fliperama86/neopico-hd/docs/GENLOCK.md

# Genlock — Implementation Analysis

## Problem

MVS runs at ~59.18 Hz. HDMI output at 60 Hz causes periodic frame repeats (~every 2s), visible as stutter in scrolling games.

---

## Option 1: Hardware Genlock (XIN Replacement)

Replace the RP2350's 12 MHz crystal with the MVS 12 MHz clock. Since the PLL is hardwired to XOSC, feeding MVS 12 MHz directly into XIN makes the entire system clock tree phase-locked to the Neo Geo — true hardware genlock with **zero software changes** to clock configuration.

### Why 12 MHz

The MVS master clock is 24 MHz; a 12 MHz derived clock is available on the board. This matches the RP2350's crystal frequency exactly, so all existing PLL divider settings (FBDIV, POSTDIV1, POSTDIV2) stay identical.

### PCB Changes

1. **Do not populate** the 12 MHz crystal
2. **Route MVS 12 MHz** to the **XIN pin** with signal conditioning:

```
MVS 12MHz ──[100R]──┬── XIN
                     │
                   [47pF]
                     │
                    GND
```

3. **XOUT**: leave floating or tie through 1M to XIN

### XOSC Configuration

Configure XOSC in bypass/external clock mode:

```c
xosc_hw->ctrl = XOSC_CTRL_FREQ_RANGE_VALUE_1_15MHZ;
hw_set_bits(&xosc_hw->ctrl, XOSC_CTRL_ENABLE_VALUE_ENABLE << XOSC_CTRL_ENABLE_LSB);
```

### What This Gets You

- **PLL_SYS config unchanged**: 12 MHz × FBDIV / POSTDIV = 126 MHz (same as today)
- **clk_sys, clk_hstx, PIO clocks** — everything phase-locked to MVS
- **Zero drift**: no frame repeats, no stutter in scrollers
- **No software genlock logic needed**
- **Audio coherence**: pixel clock and audio timing are synchronous from the first frame

### Concerns

1. **No MVS = No Boot**: Accept it, use ROSC fallback, or add a CMOS mux (SN74LVC1G3157) to switch between crystal and MVS 12 MHz.
2. **Startup Sequencing**: XOSC has a built-in stabilization counter. ROSC can serve as initial clock if there's a race.
3. **Signal Quality**: XIN accepts CMOS square waves. 100R + 47pF filters ringing. PLL VCO provides jitter filtering.
4. **Cold Boot Audio**: May improve — HDMI output is synchronous from the first frame.

---

## Option 2: Dynamic VTOTAL Modulation (Software, `NEOPICO_EXP_GENLOCK_DYNAMIC`)

Implemented, removed in the 2026-07-31 flag sunset, and **resurrected
2026-08-01** (default OFF) to fix the ~1.2 s horizontal-scroll hiccup: the
free-running ~60 Hz output beats against the 59.186 Hz MVS and repeats one
input frame per beat. The restored implementation is the bench-tuned
pre-sunset servo (wide-hysteresis ±1 vtotal acquire, constant-vtotal steady
state with a rate-limited sub-line vblank h-trim integrator), not the simple
sketch below, which is kept as the design reference.

Resurrection notes:

- Nominal vtotals: 532 (480p), 266 (240p), **751** (720p). The pre-sunset
  720p nominal 762 belonged to the deleted 372 MHz 1650-h_total timing; the
  exact-clock 1440×741 @ 64 MHz mode needs 751 (16 897.5 µs/frame vs the
  16 896.0 µs MVS frame, residual ~1.5 µs/frame, well inside the ±30 px trim
  authority of ~14.5 µs/frame over 31 vblank lines).
- scratch_x content plus the 2 KiB core-1 stack fill that bank EXACTLY; the
  genlock build therefore moves the vsync callback (which inlines the servo)
  to scratch_y via `VIDEO_PIPELINE_VSYNC_RAM` (video_pipeline.h). The
  default build keeps scratch_x placement and is byte-identical to
  pre-resurrection firmware.
- Nominals are MVS-tuned: a SNES build compiles but cannot lock to the SNES's
  ~60.10 Hz (true pre-sunset as well; SNES remains best-effort).
- Telemetry: root menu → Genlock (phase/trim/slots/vtotal/uptime + perf
  probe). Not yet hardware-validated post-resurrection; the output refresh
  becomes ~59.19 Hz, outside CTA's ±0.5 %, which the user has accepted as a
  compatibility trade-off.

The professional scan converter approach. No hardware changes needed. Measures the phase relationship between MVS and HDMI VSYNCs in real-time and modulates `v_total_lines` by ±1 to track.

### How It Works

1. On each **MVS VSYNC** (Core 0, `video_capture_run` loop), snapshot a free-running timer
2. On each **HDMI VSYNC** (Core 1, `vsync_callback`), snapshot the same timer
3. Compute phase difference: `hdmi_vsync_time - mvs_vsync_time`
4. If HDMI is ahead (phase drifting positive) → set `rt_v_total_lines = 526` for one frame (slow down)
5. If HDMI is behind (phase drifting negative) → set `rt_v_total_lines = 524` for one frame (speed up)
6. Otherwise → keep nominal `rt_v_total_lines = 525`

### Why It Works

The DMA ISR already reads `rt_v_total_lines` directly every scanline:

```c
v_scanline = (v_scanline + 1) % rt_v_total_lines;
```

Writing `rt_v_total_lines` is a single `uint16_t` store — atomic on ARM. No need to disable IRQs, rebuild command lists, or resync HSTX. The ISR picks up the new value on the next wrap.

### Implementation Sketch

```c
// Shared between cores (written by Core 0, read by Core 1)
static volatile uint32_t g_mvs_vsync_timestamp;

// Core 0 — video_capture_run(), on each MVS VSYNC:
g_mvs_vsync_timestamp = timer_hw->timerawl;

// Core 1 — vsync_callback(), on each HDMI VSYNC:
uint32_t mvs_ts = g_mvs_vsync_timestamp;
uint32_t hdmi_ts = timer_hw->timerawl;
int32_t phase_us = (int32_t)(hdmi_ts - mvs_ts);

// Dead zone prevents oscillation
#define GENLOCK_THRESHOLD_US 200
if (phase_us > GENLOCK_THRESHOLD_US) {
    rt_v_total_lines = 526;  // stretch — slow down HDMI
} else if (phase_us < -GENLOCK_THRESHOLD_US) {
    rt_v_total_lines = 524;  // shrink — speed up HDMI
} else {
    rt_v_total_lines = 525;  // nominal
}
```

### Advantages Over Static Genlock

| | Static Genlock | Dynamic VTOTAL |
|---|---|---|
| Compile-time config | Required | Not needed |
| Tracks real MVS clock | No (assumes fixed fps) | Yes (measured per-frame) |
| Handles clock drift | No | Yes |
| Pixel clock | Non-standard | Standard 25.2 MHz |
| ACR packets | Need custom CTS | Standard CTS |
| TV compatibility | Most TVs accept it | Better (standard pixel clock) |
| Visible artifact | Stutter if estimate is off | Invisible (1-line = 0.19%) |

### Design Considerations

- **Hysteresis**: The ±200µs dead zone prevents hunting. Tune on hardware — too tight causes oscillation, too wide allows visible drift before correction.
- **Max modulation**: ±1 line per frame only. Larger jumps risk visible glitch.
- **Audio packet scheduling**: `hstx_di_queue` uses `cached_v_total_lines` for audio scheduling. Keep this at nominal (525); ±1 line modulation is negligible for audio timing.
- **Phase wraparound**: Signed subtraction of uint32 handles timer wraparound naturally.
- **240p mode**: Same principle applies but with `rt_v_total_lines` based on 262 (±1 → 261 or 263).
- **Enable/disable**: Should be feature-flagged and toggleable at runtime (e.g., OSD menu option).

### Existing Infrastructure

The codebase already has everything needed:

- `video_frame_count` — HDMI frame counter (Core 1)
- `g_frame_count` — MVS frame counter (Core 0)
- `vsync_callback` — called on every HDMI VSYNC (Core 1)
- `rt_v_total_lines` — directly used in DMA ISR, writable at any time
- `timer_hw->timerawl` — free-running µs timer, accessible from both cores

---

## Option 3: Static Sysclk Match (Deleted Experiment)

Adjusted sysclk at boot to approximate the MVS frame rate. Simple, mostly worked, but:
- Not phase-locked — would still drift if the MVS clock differed from the assumed value
- Non-standard pixel clock requires custom ACR CTS
- Compile-time only — can't adapt to different boards

Removed from the firmware (dead experiment; never combined with the dynamic
VTOTAL genlock below, which was also removed after being implemented and then
not pursued further).

### Alternative: VTOTAL Match (Static, also deleted)

Kept pixel clock standard but inflated the back porch. Same limitations as
static sysclk (no feedback). Also removed.

---

## RP2350 Clock System Quick Reference

| Feature | Status | Details |
|---|---|---|
| External clock on XIN | Yes | CMOS-level, bypass mode |
| PLL FBDIV dynamic adjust | Yes | While locked, may overshoot/undershoot |
| PLL POSTDIV dynamic adjust | No | Requires unlock |
| GPIN clock input | Yes | GP12,14,20,22 — 50 MHz max, divide only |
| GPIN → PLL reference | No | PLL hardwired to XOSC/XIN |
| HSTX fractional divider | No | Integer only |
| Frequency counter (FC0) | Yes | Built-in, configurable accuracy |

## Recommendation

1. **Done (2026-08-01)**: dynamic VTOTAL modulation is back as
   `NEOPICO_EXP_GENLOCK_DYNAMIC` (default OFF; see Option 2 resurrection
   notes). Pending hardware soak before any default flip.
2. **Next PCB rev**: Add MVS 12 MHz → XIN option for true hardware genlock.
