fliperama86/neopico-hd/docs/HSTX_IMPLEMENTATION.md

# HDMI & HSTX Implementation Reference

Comprehensive record of the RP2350 HSTX implementation and HDMI audio findings.

## 1. System Architecture

- **Core 0**: Handles pixel-perfect video capture (PIO1+DMA). The stable path uses one 32K-entry RGB565 LUT. The optional Colors menu keeps two such LUTs and selects one pointer at input VSYNC, with the same one-read pixel loop. A separate default-off DARK/SHADOW experiment uses an 8.25 KiB split LUT and is timing-regressed on hardware.
- **Core 1**: Dedicated to HSTX HDMI output and the audio pipeline (polling PIO2, SRC, and TERC4 encoding).
- **Inter-core**: Single 320x240 RGB565 framebuffer + Audio Ring Buffer.

## 2. HSTX Video Pipeline

### Output Timings

- **640x480 Pixel Clock**: 25.2 MHz. The selector runs the CPU at 252 MHz and divides `clk_hstx` by 2, then the HSTX serializer by 5.
- **640x480 Line Length**: Exactly 800 pixel clocks for the VGA timing.
- **Runtime 1280x720 Pixel Clock**: exactly 64.000 MHz from a 320 MHz
  system/HSTX clock. The 1440x741 reduced-blanking raster runs at 59.979 Hz,
  uses H+/V- sync, and advertises VIC 0 with an explicit 16:9 aspect. This is
  the only 720p path; the former fixed compile-time 720p mode and its
  74.4 MHz / 372 MHz non-RT comparison path have been deleted, along with the
  experimental 960x720/1024x768 PC-monitor modes.
- **Command Lists**: Uses `HSTX_CMD_RAW_REPEAT` for blanking and `HSTX_CMD_TMDS` for active pixels.
- **NOPs**: `HSTX_CMD_NOP` separators are used to manage hardware state transitions.

### Sync Polarity

- The runtime engine tracks horizontal and vertical polarity separately.
- For a negative-polarity signal, the wire bit is low during the active pulse.
- TMDS control symbols:
  - `0x354u`: $V=0, H=0$
  - `0x0abu`: $V=0, H=1$
  - `0x154u`: $V=1, H=0$
  - `0x2abu`: $V=1, H=1$

### Stability & Scaling

- **RAW_N_SHIFTS**: Must be set to **1** in the HSTX command expander. A value of 0 actually means 32 shifts, which causes massive horizontal sync drift.
- **Line Doubling**: The 240p MVS source is scaled to 480p by doubling every line (`fb_line = dvi_line >> 1`). This ensures the full HDMI active area is filled with stable data.

### Native 240p AVI Compatibility

The native 240p output uses a non-CEA 1280x240 timing with VIC 0. Production builds define `PICO_HDMI_LEGACY_240P_AVI_INFOFRAME=1`, which emits the hardware-validated conservative AVI payload (`PB1=0x00`, `PB2=0x08`, `PR=0`). The active-format/aspect payload with `PR=3` caused black video with continuing HDMI audio on tested scaler paths. This compatibility behavior is limited to the 240p descriptor. Standard 480p retains its normal metadata, while exact-clock 720p independently uses VIC 0 with an explicit 16:9 aspect.

## 3. HDMI Audio (Data Islands)

### Encoding

- **Mode**: TERC4 (4-bit to 10-bit).
- **Structure**: 36 pixel clocks (2 Guard + 32 Packet + 2 Guard).
- **Placement**: Mode-dependent. The VGA, 240p, and PC descriptors place Data
  Islands within horizontal sync; 1280x720 uses the back porch.

### Critical Discoveries

1. **Validity Bit (V)**: MUST be set to **0 (Valid)**. Most TVs mute if $V=1$.
2. **ACR Packet**: Byte order is **Big Endian**.
   - $N = 6144$
   - $CTS = 25200$ at a 25.2 MHz pixel clock
   - $CTS = 64000$ at the exact-clock 64 MHz 720p pixel clock
3. **Throughput**: Sending packets on active video lines is required to meet the 48kHz rate (~200 packets/frame).
4. **Header Flag**: The very first symbol of the first header byte correctly omits the Data Island flag (bit 3) for compatibility.

### Pacing & Clock Accuracy

Audio packets are paced by a per-scanline accumulator in `hstx_di_queue_tick()`. The samples-per-line value is derived from the actual pixel clock and `h_total`, never from an assumed 60 Hz field rate (an early version assumed exactly 60 Hz, which over-delivered ~91 samples/s at 240p's 60.114 Hz and caused periodic dropouts; fixed in pico_hdmi `e2a4022`).

That fix still floor-truncated the value to 16.16 fixed point, delivering slightly fewer samples than the ACR-advertised rate on the same clock: about 0.18 samples/s short at 480p/240p and roughly 0.1 at the former 720p timing. Since ACR (N=6144, CTS=pixel_clock/1000, integer-exact for 25.2, 64.0, and 74.4 MHz) tells the sink to play exactly 48000 Hz, the sink's buffer drains slowly and conceals with a brief mute: a rare, TV-dependent audio drop every tens of minutes.

Since pico_hdmi `b6422ee`, `PICO_HDMI_EXACT_AUDIO_PACING` (default **ON**) carries the exact division remainder in a rational (Bresenham) accumulator, so long-term delivery equals the nominal sample rate exactly, with bounded 1/65536-sample jitter. The runtime and non-RT paths both honor this option. Rollback: build with `-DPICO_HDMI_EXACT_AUDIO_PACING=OFF`.

### Underrun Diagnostics

If the producer (Core 1 audio task) cannot keep the Data Island queue non-empty, the scanline ISR splices a pre-encoded 4-sample silence packet and increments `hstx_di_queue_silence_count`. Build with `-DNEOPICO_DIAG_AUDIO_OSD=ON` (default OFF) to display this counter as `AU<n>` on the selftest OSD screen: a counter that climbs while a drop is heard means producer starvation; a flat counter means the drop happened inside the sink.

## 4. Hardware Resource Mapping (RP2350B)

| Peripheral | Purpose | GPIO Range |
| --- | --- | --- |
| **HSTX** | HDMI Output | 12-19 |
| **PIO1** | Video Capture | 27-45 (Bank 1) |
| **PIO2** | I2S Audio | 0-2 (Bank 0) |

### External Connection Requirements

- **HDMI +5V**: Pin 18 on the HDMI connector MUST be powered with 5V.
- **Compatibility Note**: While the Morph4K may work without it, the RetroTINK and many TVs require this for signal detection.

## 5. Reference References

- `pico_lib` (Shuichi Takano): Original HDMI audio logic.
- `hsdaoh-rp2350` (Steve Markgraf): HSTX Data Island proof-of-concept.
