fliperama86/neopico-hd/docs/STREAMING_PIPELINE_PLAN.md

# NeoPico-HD: Line-Streaming Pipeline

## Current Status

**Working:** 256-line ring buffer with soft frame sync. Video stable, audio working.

**Memory:** ~241 KB BSS (down from ~417 KB original)

---

## Architecture

```
ORIGINAL (Frame-buffered + LUT):
  Core 0: Capture full frame → large LUT conversion → framebuf[320x240]
  Core 1: ISR reads framebuf → HDMI output
  Memory: ~417 KB

CURRENT (256-line ring buffer):
  Core 0: Capture line → direct RGB555→RGB565 → ring[256 lines]
  Core 1: ISR reads from ring → HDMI output
  On output VSYNC: Sync read position to latest input frame
  Memory: ~241 KB
```

---

## How It Works

### Line Ring Buffer

The ring buffer holds 256 lines (more than one full 224-line frame):

- **Core 0 (Producer):** Writes captured MVS lines sequentially
- **Core 1 (Consumer):** Reads lines for HDMI output with 2x scaling

### Frame Synchronization

At each **output VSYNC**, Core 1 syncs its read position to the latest input frame:

```c
// Called at output VSYNC
static inline void line_ring_output_vsync(void) {
    g_line_ring.read_frame_start = g_line_ring.frame_base_idx;
}
```

This approach:
- Allows independent input/output clocks (~59.6 Hz vs ~60 Hz)
- Occasionally duplicates or skips a frame to maintain sync
- No visible tearing due to full-frame buffer margin

---

## 40-Line Streaming Attempt (Shelved)

We investigated reducing the buffer to 40 lines inspired by cps2_digiav's approach.

**Motivation:** Raw performance for OSD rendering, not memory savings. A tighter streaming pipeline would provide more predictable timing and reduce memory bandwidth contention during scanline processing.

### What We Tried

1. **HSTX Hard Reset on Input VSYNC**
   - Reset HSTX shift register and clock generator via CSR.EN toggle
   - **Result:** Display lost signal entirely

2. **Soft Resync (flag only)**
   - Just sync read position without HSTX reset
   - **Result:** Flickering - 40-line buffer too small for phase variation

3. **Clock Adjustment (125 MHz)**
   - Slow output to ~59.5 Hz so it trails input
   - **Result:** Still flickering - phase mismatch within frames

### Why It Failed

The fundamental issue: with only 40 lines of buffer, the phase relationship between input and output VSYNC must be tightly controlled. Without hardware genlock:

- Output VSYNC timing is independent of input
- Phase can drift by tens of lines within a frame
- 40 lines isn't enough margin for worst-case phase offset

### cps2_digiav Difference

cps2_digiav uses an FPGA with precise control over output timing. Their `V_STARTLINE` mechanism can instantly reposition the output scanline counter. The RP2350's HSTX doesn't support mid-stream repositioning without losing signal.

### Future Options

If 40-line streaming is revisited:
1. **PLL-based genlock:** Lock output pixel clock to input (complex)
2. **Frame skip detection:** Predict phase and pre-adjust
3. **Larger minimum buffer:** Find the threshold (64? 80? 128 lines?)

---

## Memory Budget

| Component | Size |
|---|---|
| line_ring (256 lines) | 164 KB |
| Audio buffers | ~8 KB |
| Other (stacks, DMA, etc.) | ~69 KB |
| **Total BSS** | **~241 KB** |

The RP2350 has 520 KB SRAM, leaving ~279 KB free for future features (OSD, settings, etc.).

---

## Files

| File | Purpose |
|---|---|
| `src/video/line_ring.h` | Ring buffer API and data structure |
| `src/video/video_capture.c` | Core 0 capture loop, writes to ring |
| `lib/pico_hdmi/src/video_output.c` | Core 1 HDMI output, reads from ring |
| `src/main.c` | Scanline callback with 2x scaling |

---

## DARK/SHADOW Status

Current implementation:

1. PIO capture preserves 19 bits including SHADOW and DARK.
2. Default build (`NEOPICO_ENABLE_DARK_SHADOW=OFF`) uses a 32K-entry RGB LUT path and does not apply the captured SHADOW/DARK flags.
3. Whenever DARK/SHADOW is off (MVS builds), the live persistent Colors menu adds `Digital` and `Analog` normal-color choices. Two 64 KiB tables are generated at boot, and browsing previews through one frame-stable pointer selected at input VSYNC. SELECT restores the committed model; START/MENU persists the preview. The pixel loop still performs one LUT read and ignores SHADOW/DARK.
4. Separate `NEOPICO_ENABLE_DARK_SHADOW=ON` uses an 8,448-byte split RGB565 LUT with four independent states. Hardware testing showed bottom-screen pixel jitter, so it remains default off; enabling it automatically compiles out the Colors menu (the two features share the same capture LUT machinery).
