fliperama86/neopico-hd/src/video/line_ring.h

#ifndef LINE_RING_H
#define LINE_RING_H

#include "hardware/sync.h"

#include <stdbool.h>
#include <stdint.h>

#include "capture_profile.h"

// Line buffer configuration. Fixed board/tuning constant, not a build
// variant (was NEOPICO_LINE_RING_SIZE; see AGENTS.md flag-sunset notes).
#define NEOPICO_LINE_RING_SIZE 256

#define LINE_RING_SIZE NEOPICO_LINE_RING_SIZE
#define LINE_WIDTH CAPTURE_FRAME_WIDTH
#define LINES_PER_FRAME CAPTURE_ACTIVE_HEIGHT

typedef struct {
    uint16_t lines[LINE_RING_SIZE][LINE_WIDTH]; // ~25KB line buffer

#if NEOPICO_EXP_RGB888_SCANOUT
    // RGB888 scanout stores raw entropy (DARK + raw RGB555) in the 16 bits
    // above, which leaves no room for SHADOW. SHADOW is a screen-wide control
    // (system latch bit 0), so one flag per line is faithful and costs 256 B.
    uint8_t line_shadow[LINE_RING_SIZE];
#endif

    // Core 0 (producer) state
    volatile uint32_t write_idx;      // Global write position (lines written total)
    volatile uint32_t frame_base_idx; // Global index where current frame starts

    // Core 1 (consumer) state
    volatile uint32_t read_frame_start; // Global index of display frame start

    // Resync flag - Core 0 requests, Core 1 executes
    volatile bool resync_pending;
} line_ring_t;

extern line_ring_t g_line_ring;

// ============================================================================
// Diagnostic counters (NEOPICO_DIAG_COUNTERS, default OFF) — capture-health
// instrumentation for the 720p glitch investigation. Dumped over USB-serial.
// ============================================================================
#ifndef NEOPICO_DIAG_COUNTERS
#define NEOPICO_DIAG_COUNTERS 0
#endif

#if NEOPICO_DIAG_COUNTERS
typedef struct {
    volatile uint32_t not_written; // Core 1 wanted a line the producer hadn't written yet
    volatile uint32_t overrun;     // Core 1 wanted a line already overwritten (ring wrap)
    volatile uint32_t out_frames;  // Core 1 output VSYNCs
    volatile uint32_t sync_resets; // Core 0 capture hardware resets (MVS signal loss)
} line_ring_diag_t;
extern line_ring_diag_t g_line_ring_diag;
#endif

// ============================================================================
// Core 0 API (Producer) - Input capture side
// ============================================================================

// Called at input VSYNC - request HSTX resync
static inline void line_ring_vsync(void)
{
    // Mark start of new frame
    g_line_ring.frame_base_idx = g_line_ring.write_idx;
    __dmb();
    // Request Core 1 to resync HSTX
    g_line_ring.resync_pending = true;
}

// Get write pointer for line N within current frame
static inline uint16_t *line_ring_write_ptr(uint16_t line)
{
    uint32_t idx = g_line_ring.frame_base_idx + line;
    return g_line_ring.lines[idx % LINE_RING_SIZE];
}

// Signal that lines 0..(total_lines-1) of current frame are written
static inline void line_ring_commit(uint16_t total_lines)
{
    __dmb(); // Ensure line data visible before updating index
    g_line_ring.write_idx = g_line_ring.frame_base_idx + total_lines;
}

// ============================================================================
// Core 1 API (Consumer) - HDMI output side
// ============================================================================

// Check if resync is requested (called from DMA ISR)
// Only clears the flag - actual sync happens at output VSYNC via line_ring_output_vsync()
static inline bool line_ring_should_resync(void)
{
    if (g_line_ring.resync_pending) {
        g_line_ring.resync_pending = false;
        return true;
    }
    return false;
}

// Called at output VSYNC (when not resyncing)
static inline void line_ring_output_vsync(void)
{
    uint32_t frame_start = g_line_ring.frame_base_idx;
    __dmb();
    const uint32_t write_pos = g_line_ring.write_idx;

    // Core 0 publishes the new frame base before it commits line 0. If HDMI
    // lands in that short window, retain the previous complete frame instead
    // of selecting an empty frame and emitting fallback-colored lines.
    if (write_pos == frame_start && frame_start >= LINES_PER_FRAME) {
        frame_start -= LINES_PER_FRAME;
    }
    g_line_ring.read_frame_start = frame_start;
    __dmb();
#if NEOPICO_DIAG_COUNTERS
    g_line_ring_diag.out_frames++;
#endif
}

// Check if line is ready and still in buffer
static inline bool line_ring_ready(uint16_t line)
{
    uint32_t target_idx = g_line_ring.read_frame_start + line;
    uint32_t write_pos = g_line_ring.write_idx;

    // Line must have been written
    if (target_idx >= write_pos) {
#if NEOPICO_DIAG_COUNTERS
        g_line_ring_diag.not_written++;
#endif
        return false; // Not written yet
    }

    // Line must still be in buffer (not overwritten)
    if (write_pos - target_idx > LINE_RING_SIZE) {
#if NEOPICO_DIAG_COUNTERS
        g_line_ring_diag.overrun++;
#endif
        return false; // Buffer overrun - data was overwritten
    }

    return true;
}

// Get read pointer for line N in current display frame
static inline const uint16_t *line_ring_read_ptr(uint16_t line)
{
    __dmb(); // Ensure we see latest committed data
    uint32_t target_idx = g_line_ring.read_frame_start + line;
    return g_line_ring.lines[target_idx % LINE_RING_SIZE];
}

#if NEOPICO_EXP_RGB888_SCANOUT
static inline void line_ring_write_shadow(uint16_t line, uint32_t shadow)
{
    uint32_t target_idx = g_line_ring.frame_base_idx + line;
    g_line_ring.line_shadow[target_idx % LINE_RING_SIZE] = (uint8_t)(shadow & 1U);
}

static inline uint32_t line_ring_read_shadow(uint16_t line)
{
    uint32_t target_idx = g_line_ring.read_frame_start + line;
    return g_line_ring.line_shadow[target_idx % LINE_RING_SIZE];
}
#endif

#endif // LINE_RING_H
