fliperama86/neopico-hd/src/misc/debug_render.c

#include "debug_render.h"
#include <string.h>

// Standard 5x7 font (ASCII 32-126)
static const uint8_t font_5x7[] = {
    0x00, 0x00, 0x00, 0x00, 0x00, // 32 space
    0x00, 0x00, 0x5f, 0x00, 0x00, // 33 !
    0x00, 0x07, 0x00, 0x07, 0x00, // 34 "
    0x14, 0x7f, 0x14, 0x7f, 0x14, // 35 #
    0x24, 0x2a, 0x7f, 0x2a, 0x12, // 36 $
    0x23, 0x13, 0x08, 0x64, 0x62, // 37 %
    0x36, 0x49, 0x55, 0x22, 0x50, // 38 &
    0x00, 0x05, 0x03, 0x00, 0x00, // 39 '
    0x00, 0x1c, 0x22, 0x41, 0x00, // 40 (
    0x00, 0x41, 0x22, 0x1c, 0x00, // 41 )
    0x14, 0x08, 0x3e, 0x08, 0x14, // 42 *
    0x08, 0x08, 0x3e, 0x08, 0x08, // 43 +
    0x00, 0x50, 0x30, 0x00, 0x00, // 44 ,
    0x08, 0x08, 0x08, 0x08, 0x08, // 45 -
    0x00, 0x60, 0x60, 0x00, 0x00, // 46 .
    0x20, 0x10, 0x08, 0x04, 0x02, // 47 /
    0x3e, 0x51, 0x49, 0x45, 0x3e, // 48 0
    0x00, 0x42, 0x7f, 0x40, 0x00, // 49 1
    0x42, 0x61, 0x51, 0x49, 0x46, // 50 2
    0x21, 0x41, 0x45, 0x4b, 0x31, // 51 3
    0x18, 0x14, 0x12, 0x7f, 0x10, // 52 4
    0x27, 0x45, 0x45, 0x45, 0x39, // 53 5
    0x3c, 0x4a, 0x49, 0x49, 0x30, // 54 6
    0x01, 0x71, 0x09, 0x05, 0x03, // 55 7
    0x36, 0x49, 0x49, 0x49, 0x36, // 56 8
    0x06, 0x49, 0x49, 0x29, 0x1e, // 57 9
    0x00, 0x36, 0x36, 0x00, 0x00, // 58 :
    0x00, 0x56, 0x36, 0x00, 0x00, // 59 ;
    0x08, 0x14, 0x22, 0x41, 0x00, // 60 <
    0x14, 0x14, 0x14, 0x14, 0x14, // 61 =
    0x00, 0x41, 0x22, 0x14, 0x08, // 62 >
    0x02, 0x01, 0x51, 0x09, 0x06, // 63 ?
    0x32, 0x49, 0x79, 0x41, 0x3e, // 64 @
    0x7e, 0x11, 0x11, 0x11, 0x7e, // 65 A
    0x7f, 0x49, 0x49, 0x49, 0x36, // 66 B
    0x3e, 0x41, 0x41, 0x41, 0x22, // 67 C
    0x7f, 0x41, 0x41, 0x22, 0x1c, // 68 D
    0x7f, 0x49, 0x49, 0x49, 0x41, // 69 E
    0x7f, 0x09, 0x09, 0x09, 0x01, // 70 F
    0x3e, 0x41, 0x49, 0x49, 0x7a, // 71 G
    0x7f, 0x08, 0x08, 0x08, 0x7f, // 72 H
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
};

void debug_draw_char(uint16_t *fb, uint fb_w, uint fb_h, int x, int y, char c, uint16_t color, uint16_t bg) {
    if (c < 32 || c > 126) c = ' ';
    int idx = (c - 32) * 5;
    
    // Scale factor 1x for native 5x7 pixels on 320x240
    const int scale = 1;

    for (int col = 0; col < 5; col++) {
        uint8_t line = font_5x7[idx + col];
        for (int row = 0; row < 8; row++) {
            bool active = (line >> row) & 0x1;
            uint16_t draw_color = active ? color : bg;
            
            // Draw a 1x1 native pixel
            if (active || bg != color) {
                int px = x + col;
                int py = y + row;
                if (px < (int)fb_w && py < (int)fb_h) {
                    fb[py * fb_w + px] = draw_color;
                }
            }
        }
    }
}

void debug_draw_string(uint16_t *fb, uint fb_w, uint fb_h, int x, int y, const char *str, uint16_t color, uint16_t bg) {
    while (*str) {
        char c = *str++;
        // Force ALL CAPS for maximum legibility
        if (c >= 'a' && c <= 'z') c -= 32;
        debug_draw_char(fb, fb_w, fb_h, x, y, c, color, bg);
        x += 6; // 5 columns + 1 spacing
        if (x + 6 > (int)fb_w) break;
    }
}
